m24h/sony_ttl_flash_D316i/circuit/2D_PCB1_top.png

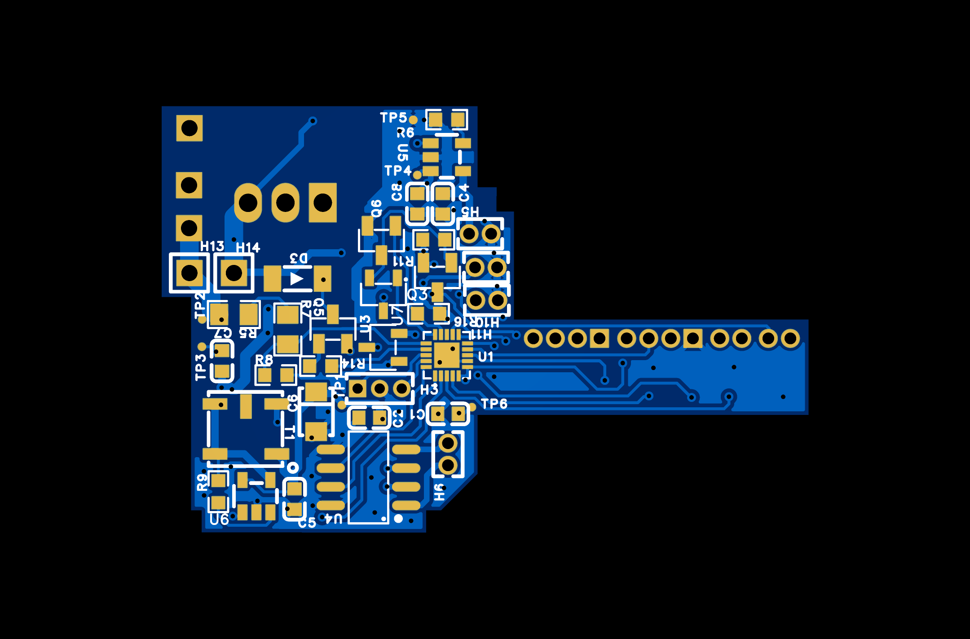
circuit/2D_PCB1_top.png
