m24h/sony_ttl_flash_D316i/practice/1.jpg

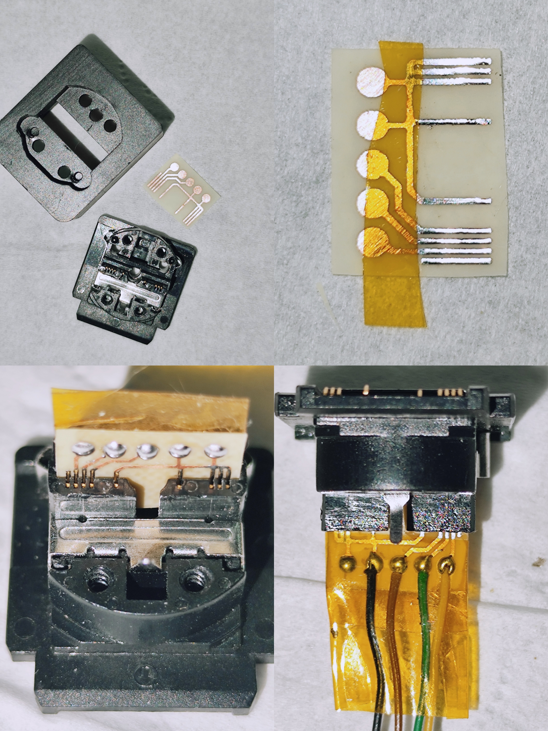
practice/1.jpg
