m24h/sony_ttl_flash_D316i/practice/2.jpg

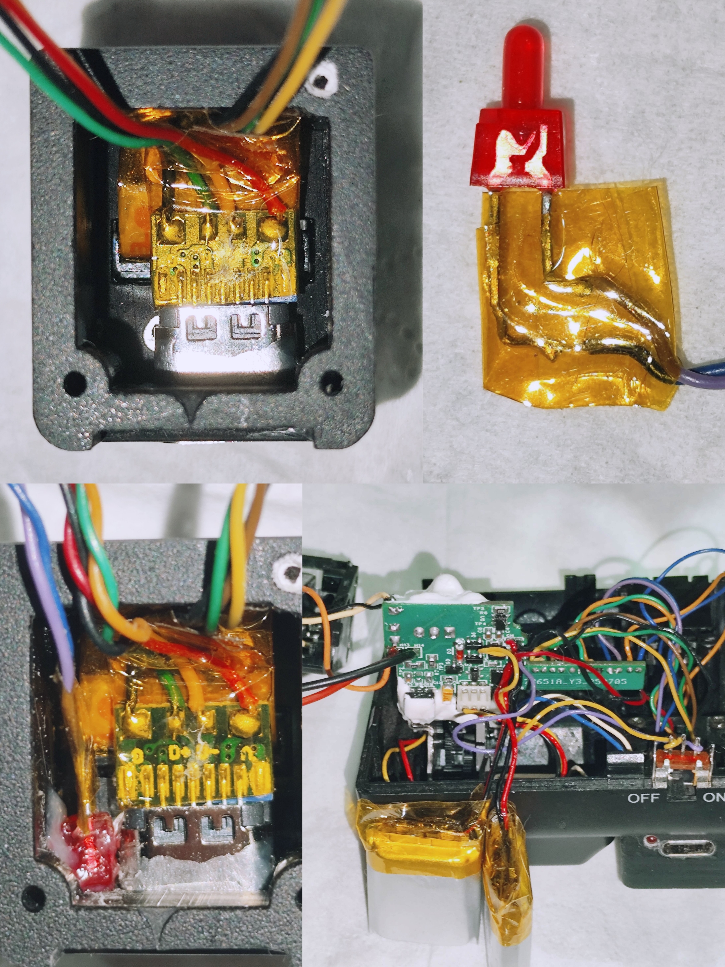
practice/2.jpg
