m24h/sony_ttl_flash_D316i/practice/3.jpg

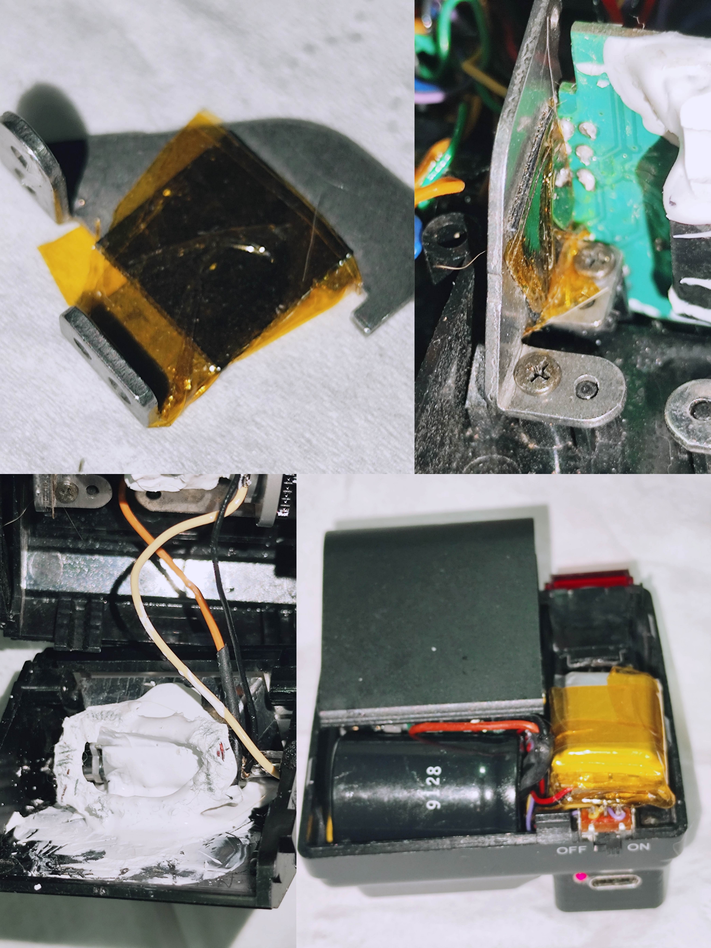
practice/3.jpg
