m24h/sony_ttl_flash_D316i/practice/4.jpg

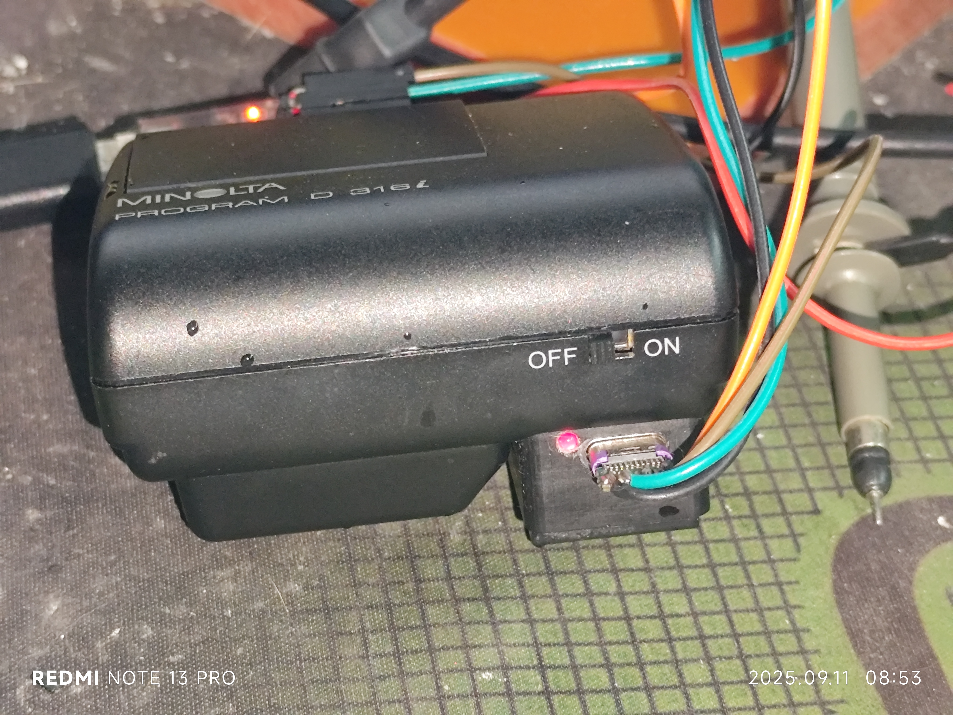
practice/4.jpg
